Solderingironspb/ModbusRTU_Master_MQTT_Gateway/Project1_Опрос_электросчетчика_ABB_E31/CH32V203F8P6/Clean_project/Core/Src/ModbusRTU.c

/*
 * ModbusRTU.c
 *
 *  Библиотека для работы по протоколу ModbusRTU в режиме Master.
 *  Функции: формировать запрос, вычислять CRC16.
 *
 *  Created on: Nov 16, 2021
 *      Author: Oleg Volkov
 */

#ifndef SRC_MODBUSRTU_C_
#define SRC_MODBUSRTU_C_

#include "main.h"
#include "ModbusRTU.h"

uint8_t ModbusRTU_tx_buffer[ModbusRTU_TX_BUFFER_SIZE] = { 0, };
//uint8_t ModbusRTU_rx_buffer[ModbusRTU_RX_BUFFER_SIZE] = { 0, };

/*--------------------------------Добавить в main.c-------------------------------*/
//extern uint8_t ModbusRTU_tx_buffer[64];
//extern uint8_t ModbusRTU_rx_buffer[256];
/*--------------------------------Добавить в main.c-------------------------------*/

/*------------------------------CRC16(ModbusRTU)----------------------------------*/
uint16_t ModbusRTU_CRC16_Calculate(uint8_t *data, uint8_t lenght, uint8_t byte_order) {
///Функция рассчета CRC16.
/// \param *data - массив данных
///	\param lenght - длина массива данных
/// \param byte_order - порядок байт:
///2 - ABDC(младшим регистром вперед, младшим байтом вперед),
///3 - DCAB(старшим регистром вперед, младшим байтом вперед),
///4 - BACD(младшим регистром вперед, старшим байтом вперед),
///5 - DCBA(старшим регистром вперед, старшим байтом вперед).

    uint16_t crc = 0xFFFF;
    while (lenght--) {
        crc ^= *data++;
        for (int i = 0; i < 8; i++) {
            if (crc & 0x01) {
                crc = (crc >> 1u) ^ 0xA001;
            } else {
                crc = crc >> 1u;
            }
        }
    }
    switch (byte_order) {
        case (BYTE_ORDER_AB_CD): //ABCD(младшим регистром вперед, младшим байтом вперед),
            break;
        case (BYTE_ORDER_CD_AB): //DCAB(старшим регистром вперед, младшим байтом вперед),
            crc = (crc << 8u) | (crc >> 8u);
            break;
        case (BYTE_ORDER_BA_DC): //BACD(младшим регистром вперед, старшим байтом вперед),
            crc = (((crc >> 8u) & 0x0F) << 12u) | ((crc >> 12u) << 8u) | ((crc << 12u) << 4u) | ((crc >> 4u) & 0x00F);
            break;
        case (BYTE_ORDER_DC_BA): //DCBA(старшим регистром вперед, старшим байтом вперед).
            crc = (((crc >> 8u) & 0x0F) << 4u) | (crc >> 12u) | ((crc << 12u) << 12u) | (((crc >> 4u) & 0x00F) << 8u);
            break;
    }
    return crc;
}
/*------------------------------CRC16(ModbusRTU)----------------------------------*/

/*------------------------------Проверка CRC16 входящего пакета данных----------------------------*/
//bool ModbusRTU_CRC16_Check(USART_TypeDef* USART) {
/////Функция проверки CRC16 входящего пакета данных.
/////Если CRC16 входящего пакета равна CRC16, содержащейся в пакете - Данные целые. Функция вернет true. В противном случае false.
///// \param *huart - UART, по которому принимаем данные.
//    uint16_t CRC_check = ModbusRTU_CRC16_Calculate(ModbusRTU_rx_buffer, len - 2, 1); //Считаем CRC входящих данных
//    uint16_t CRC_rx_buffer = ModbusRTU_rx_buffer[len - 2] << 8u | ModbusRTU_rx_buffer[len - 1]; //Смотрим CRC, которая была в пакете
//
//    if (CRC_check == CRC_rx_buffer) {
//        return true;
//    } else {
//        return false;
//    }
//}
/*------------------------------Проверка CRC16 входящего пакета данных----------------------------*/

/*------------------------------------Функция 0x01 Read Coils----------------------------------- */
void ModbusRTU_Read_Coils_0x01(uint8_t Slave_ID, uint16_t Read_adress, uint16_t Quantity, uint8_t Slave_byte_order) {
///Функция 0x01 Read Coils
/// \param Slave_ID - ID Modbus RTU Slave устройства, к которому обращаемся
/// \param Read_adress - Адрес, с которого начинаем чтение данных
/// \param Quantity - количество запрашиваемых 16ти битных данных.
    //Quantity должен быть от 1 до 2000.
/// \param Slave_byte_order - Порядок регистра и байт в ModbusRTU Slave устройстве

    ModbusRTU_tx_buffer[0] = Slave_ID;
    ModbusRTU_tx_buffer[1] = 0x01;
    ModbusRTU_tx_buffer[2] = (uint16_t) Read_adress >> 8u;
    ModbusRTU_tx_buffer[3] = (uint16_t) Read_adress & 0x00FF;
    ModbusRTU_tx_buffer[4] = (uint16_t) Quantity >> 8u;
    ModbusRTU_tx_buffer[5] = (uint16_t) Quantity & 0x00FF;
    uint16_t CRC16 = ModbusRTU_CRC16_Calculate(ModbusRTU_tx_buffer, 6, Slave_byte_order);
    ModbusRTU_tx_buffer[6] = (uint16_t) CRC16 >> 8u;
    ModbusRTU_tx_buffer[7] = (uint16_t) CRC16 & 0x00FF;
    ModbusRTU_Transmit(USART2, ModbusRTU_tx_buffer, 8, 100);
}
/*------------------------------------Функция 0x01 Read Coils----------------------------------- */

/*--------------------------------Функция 0x02 Read Discrete Inputs----------------------------- */
void ModbusRTU_Read_Discrete_Inputs_0x02(uint8_t Slave_ID, uint16_t Read_adress, uint16_t Quantity, uint8_t Slave_byte_order) {
///Функция 0x02 Read Discrete Inputs
/// \param Slave_ID - ID Modbus RTU Slave устройства, к которому обращаемся
/// \param Read_adress - Адрес, с которого начинаем чтение данных
/// \param Quantity - количество запрашиваемых 16ти битных данных.
    //Quantity должен быть от 1 до 2000.
/// \param Slave_byte_order - Порядок регистра и байт в ModbusRTU Slave устройстве

    ModbusRTU_tx_buffer[0] = Slave_ID;
    ModbusRTU_tx_buffer[1] = 0x02;
    ModbusRTU_tx_buffer[2] = (uint16_t) Read_adress >> 8u;
    ModbusRTU_tx_buffer[3] = (uint16_t) Read_adress & 0x00FF;
    ModbusRTU_tx_buffer[4] = (uint16_t) Quantity >> 8u;
    ModbusRTU_tx_buffer[5] = (uint16_t) Quantity & 0x00FF;
    uint16_t CRC16 = ModbusRTU_CRC16_Calculate(ModbusRTU_tx_buffer, 6, Slave_byte_order);
    ModbusRTU_tx_buffer[6] = (uint16_t) CRC16 >> 8u;
    ModbusRTU_tx_buffer[7] = (uint16_t) CRC16 & 0x00FF;
    ModbusRTU_Transmit(USART2, ModbusRTU_tx_buffer, 8, 100);
}
/*--------------------------------Функция 0x02 Read Discrete Inputs----------------------------- */

/*------------------------------Функция 0x03 Read Holding Registers----------------------------- */
void ModbusRTU_Read_Holding_Registers_0x03(uint8_t Slave_ID, uint16_t Read_adress, uint8_t Quantity, uint8_t Slave_byte_order) {
///Функция 0x03 Read Holding Registers
/// \param Slave_ID - ID Modbus RTU Slave устройства, к которому обращаемся
/// \param Read_adress - Адрес, с которого начинаем чтение данных
/// \param Quantity - количество запрашиваемых 16ти битных данных. Если мы запрашиваем Float, то Quantity кратно 2, т.е. 32 бита. 2 Float переменные - соответственно Quantity = 4. И т.д.
    //Quantity должен быть от 1 до 125.
/// \param Slave_byte_order - Порядок регистра и байт в ModbusRTU Slave устройстве

    ModbusRTU_tx_buffer[0] = Slave_ID;
    ModbusRTU_tx_buffer[1] = 0x03;
    ModbusRTU_tx_buffer[2] = (uint16_t) Read_adress >> 8u;
    ModbusRTU_tx_buffer[3] = (uint16_t) Read_adress & 0x00FF;
    ModbusRTU_tx_buffer[4] = 0x00;
    ModbusRTU_tx_buffer[5] = Quantity;
    uint16_t CRC16 = ModbusRTU_CRC16_Calculate(ModbusRTU_tx_buffer, 6, Slave_byte_order);
    ModbusRTU_tx_buffer[6] = (uint16_t) CRC16 >> 8u;
    ModbusRTU_tx_buffer[7] = (uint16_t) CRC16 & 0x00FF;
    ModbusRTU_Transmit(USART2, ModbusRTU_tx_buffer, 8, 100);
}
/*------------------------------Функция 0x03 Read Holding Registers----------------------------- */

/*--------------------------------Функция 0x04 Read Input Registers----------------------------- */
void ModbusRTU_Read_Input_Registers_0x04(uint8_t Slave_ID, uint16_t Read_adress, uint8_t Quantity, uint8_t Slave_byte_order) {
///Функция 0x04 Read Discrete Inputs
/// \param Slave_ID - ID Modbus RTU Slave устройства, к которому обращаемся
/// \param Read_adress - Адрес, с которого начинаем чтение данных
/// \param Quantity - количество запрашиваемых 16ти битных данных.
    //Quantity должен быть от 1 до 125.
/// \param Slave_byte_order - Порядок регистра и байт в ModbusRTU Slave устройстве

    ModbusRTU_tx_buffer[0] = Slave_ID;
    ModbusRTU_tx_buffer[1] = 0x04;
    ModbusRTU_tx_buffer[2] = (uint16_t) Read_adress >> 8u;
    ModbusRTU_tx_buffer[3] = (uint16_t) Read_adress & 0x00FF;
    ModbusRTU_tx_buffer[4] = 0x00;
    ModbusRTU_tx_buffer[5] = Quantity;
    uint16_t CRC16 = ModbusRTU_CRC16_Calculate(ModbusRTU_tx_buffer, 6, Slave_byte_order);
    ModbusRTU_tx_buffer[6] = (uint16_t) CRC16 >> 8u;
    ModbusRTU_tx_buffer[7] = (uint16_t) CRC16 & 0x00FF;
    ModbusRTU_Transmit(USART2, ModbusRTU_tx_buffer, 8, 100);
}
/*--------------------------------Функция 00x04 Read Input Registers----------------------------- */

/*--------------------------------------------Функция 0x10 Preset Multiple Registers---------------------------------------------*/
uint8_t ModbusRTU_Preset_Multiple_Registers_0x10(uint8_t Slave_ID, uint16_t Write_adress, uint16_t Quantity_registers, int16_t *value, uint8_t Slave_byte_order) {
///Функция 0x10 Preset Multiple Registers(собирает массив данных на запрос по ModbusRTU и возвращает длинну собранного буфера данных)
/// \param Slave_ID - ID Modbus RTU Slave устройства, к которому обращаемся
/// \param Write_adress - Адрес, с которого начинаем запись данных
/// \param Quantity_registers - количество запрашиваемых 16ти битных ячеек, куда будем кидать данные.
// Обратите внимание, что далеко не все контроллеры поддерживают множественную запись, а довольствуются записью по-одному параметру.
/// \param *value - указатель на данные, которые будем отправлять. Лучше всего работать с массивом данных.
/// \param Slave_byte_order - Порядок регистра и байт в ModbusRTU Slave устройстве
    uint8_t buffer_size = 0;
    ModbusRTU_tx_buffer[0] = Slave_ID;
    ModbusRTU_tx_buffer[1] = 0x10;
    ModbusRTU_tx_buffer[2] = *((uint8_t*) &Write_adress + 1);
    ModbusRTU_tx_buffer[3] = *(uint8_t*) &Write_adress;
    ModbusRTU_tx_buffer[4] = *((uint8_t*) &Quantity_registers + 1);
    ModbusRTU_tx_buffer[5] = *(uint8_t*) &Quantity_registers;
    ModbusRTU_tx_buffer[6] = Quantity_registers * 2;
    for (uint8_t i = 0; i < Quantity_registers; i++) {
        ModbusRTU_tx_buffer[7 + (i * 2)] = *((int8_t*) value + (1 + (i * 2)));
        ModbusRTU_tx_buffer[8 + (i * 2)] = *((int8_t*) value + (i * 2));
        buffer_size = 8 + (i * 2) + 1;
    }
    uint16_t CRC16 = ModbusRTU_CRC16_Calculate(ModbusRTU_tx_buffer, buffer_size, Slave_byte_order);
    ModbusRTU_tx_buffer[buffer_size] = *((uint8_t*) &CRC16 + 1);
    ModbusRTU_tx_buffer[buffer_size + 1] = *(uint8_t*) &CRC16;
    buffer_size = buffer_size + 2;
    ModbusRTU_Transmit(USART2, ModbusRTU_tx_buffer, buffer_size, 100);
    return buffer_size;
}
/*--------------------------------------------Функция 0x10 Preset Multiple Registers---------------------------------------------*/

float ModbusRTU_GetData_Float(uint8_t* data_massive, uint8_t start_data_address, uint8_t Slave_byte_order) {
    uint32_t Data = 0;
    switch (Slave_byte_order) {
        case BYTE_ORDER_AB_CD:
            Data = (data_massive[start_data_address] << 24U) | (data_massive[start_data_address + 1] << 16U) | (data_massive[start_data_address + 2] << 8U) | (data_massive[start_data_address + 3]);
            break;
        case BYTE_ORDER_CD_AB:
            Data = (data_massive[start_data_address + 2] << 24U) | (data_massive[start_data_address + 3] << 16U) | (data_massive[start_data_address] << 8U) | (data_massive[start_data_address + 1]);
            break;
        case BYTE_ORDER_BA_DC:
            Data = (data_massive[start_data_address + 1] << 24U) | (data_massive[start_data_address] << 16U) | (data_massive[start_data_address + 3] << 8U) | (data_massive[start_data_address + 2]);
            break;
        case BYTE_ORDER_DC_BA:
            Data = (data_massive[start_data_address + 3] << 24U) | (data_massive[start_data_address + 2] << 16U) | (data_massive[start_data_address + 1] << 8U) | (data_massive[start_data_address]);
            break;
    }
    return *((float*) &Data);
}

uint32_t ModbusRTU_GetData_U32(uint8_t* data_massive, uint8_t start_data_address, uint8_t Slave_byte_order) {
    uint32_t Data = 0;
    switch (Slave_byte_order) {
        case BYTE_ORDER_AB_CD:
            Data = (data_massive[start_data_address] << 24U) | (data_massive[start_data_address + 1] << 16U) | (data_massive[start_data_address + 2] << 8U) | (data_massive[start_data_address + 3]);
            break;
        case BYTE_ORDER_CD_AB:
            Data = (data_massive[start_data_address + 2] << 24U) | (data_massive[start_data_address + 3] << 16U) | (data_massive[start_data_address] << 8U) | (data_massive[start_data_address + 1]);
            break;
        case BYTE_ORDER_BA_DC:
            Data = (data_massive[start_data_address + 1] << 24U) | (data_massive[start_data_address] << 16U) | (data_massive[start_data_address + 3] << 8U) | (data_massive[start_data_address + 2]);
            break;
        case BYTE_ORDER_DC_BA:
            Data = (data_massive[start_data_address + 3] << 24U) | (data_massive[start_data_address + 2] << 16U) | (data_massive[start_data_address + 1] << 8U) | (data_massive[start_data_address]);
            break;
    }
    return Data;
}

uint16_t ModbusRTU_GetData_U16(uint8_t* data_massive, uint8_t start_data_address, uint8_t slave_byte_order) {
    uint16_t Data = 0;
    switch (slave_byte_order) {
        case BYTE_ORDER_AB:
            Data = (data_massive[start_data_address] << 8) | data_massive[start_data_address + 1];
            break;
        case BYTE_ORDER_BA:
            Data = (data_massive[start_data_address + 1] << 8) | data_massive[start_data_address];
            break;
    }
    return Data;
}

uint32_t ModbusRTU_Float_to_U32_convert(float* data, uint8_t slave_byte_order) {
    uint32_t Data = 0;
    Data = *((uint32_t*) data);
    switch (slave_byte_order) {
        case BYTE_ORDER_AB_CD:
            Data = (*((uint8_t*)&Data + 3) << 24) | (*((uint8_t*)&Data + 2) << 16) | (*((uint8_t*)&Data + 1) << 8) | (*((uint8_t*)&Data));
            break;
        case BYTE_ORDER_CD_AB:
            Data = (*((uint8_t*)&Data + 1) << 24) | (*((uint8_t*)&Data) << 16) | (*((uint8_t*)&Data + 3) << 8) | (*((uint8_t*)&Data + 2));
            break;
        case BYTE_ORDER_BA_DC:
            Data = (*((uint8_t*)&Data + 2) << 24) | (*((uint8_t*)&Data + 3) << 16) | (*((uint8_t*)&Data) << 8) | (*((uint8_t*)&Data + 1));
            break;
        case BYTE_ORDER_DC_BA:
            Data = (*((uint8_t*)&Data) << 24) | (*((uint8_t*)&Data + 1) << 16) | (*((uint8_t*)&Data + 2) << 8) | (*((uint8_t*)&Data + 3));
            break;
    }
    return Data;
}

#endif /* SRC_MODBUSRTU_C_ */
